rassweiler/pi-networked-counter/Models/NetworkCounter_Adapter_9mmHorizontal_9mmVertical.FCStd

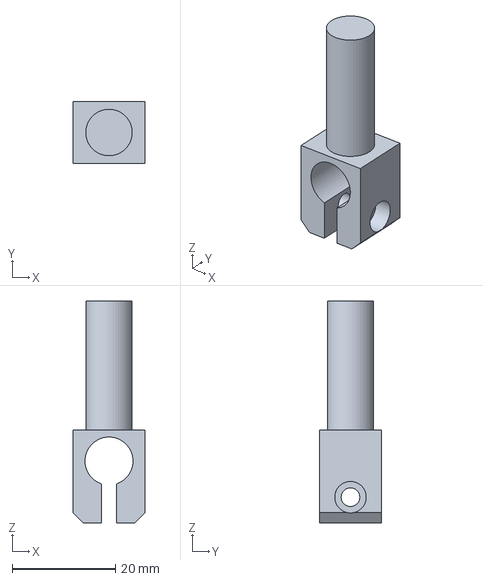
[picture p21: CAD file, 2025-04-04]
Models/NetworkCounter_Adapter_9mmHorizontal_9mmVertical.FCStd
14.0 x 12.0 x 43.0 mm
